NGliese/creditcard_cv_showoff/main/Components/lcd_display/include/lcd_data.hpp

#ifndef main_Components_lcd_display_include_lcd_data_hpp
#define main_Components_lcd_display_include_lcd_data_hpp

#include <stdint.h>


uint8_t HelloWorld[512] = {
0xFF, 0xFF, 0xFF, 0xFF, 0xFF, 0xFF, 0xFF, 0xFF, 0xFF, 0xFF, 0xFF, 0xFF, 0xFF, 0xFF, 0xFF, 0xFF,
0xFF, 0xFF, 0xFF, 0xFF, 0xFF, 0xFF, 0xFF, 0xFF, 0xFF, 0xFF, 0xFF, 0xFF, 0xFF, 0xFF, 0xFF, 0xFF,
0xFF, 0xFF, 0xFF, 0xFF, 0xFF, 0xFF, 0xFF, 0xFF, 0xFF, 0xFF, 0xFF, 0xFF, 0xFF, 0xFF, 0xFF, 0xFF,
0xFF, 0xFF, 0xFF, 0xFF, 0xFF, 0xFF, 0xFF, 0xFF, 0xFF, 0xFF, 0xFF, 0xFF, 0xFF, 0xFF, 0xFF, 0xFF,
0xFF, 0xFF, 0xFF, 0xFF, 0xFF, 0xFF, 0xFF, 0xFF, 0xFF, 0xFF, 0xFF, 0xFF, 0xFF, 0xFF, 0xFF, 0xFF,
0xFF, 0xFF, 0xFF, 0xFF, 0xFF, 0xFF, 0xFF, 0xFF, 0xFF, 0xFF, 0xFF, 0xFF, 0xFF, 0xFF, 0xFF, 0xFF,
0xFF, 0xFF, 0xFF, 0xFF, 0xFF, 0xFF, 0xFF, 0xFF, 0xFF, 0xFF, 0xFF, 0xFF, 0xFF, 0xFF, 0xFF, 0xFF,
0xFF, 0xFF, 0xFF, 0xFF, 0xFF, 0xFF, 0xFF, 0xFF, 0xFF, 0xFF, 0xFF, 0xFF, 0xFF, 0xFF, 0xFF, 0xFF,
0xFF, 0xFF, 0xFF, 0xFF, 0xFF, 0xFF, 0xFF, 0xFF, 0x07, 0x07, 0x07, 0x07, 0xC7, 0xC7, 0x07, 0x07,
0x07, 0x07, 0xC7, 0xC7, 0x07, 0x07, 0xC7, 0xC7, 0x47, 0x47, 0x4F, 0x4F, 0x0F, 0x0F, 0xCF, 0xCF,
0x0F, 0x0F, 0x0F, 0x0F, 0x0F, 0x0F, 0xCF, 0xCF, 0x0F, 0x0F, 0x0F, 0x0F, 0x0F, 0x0F, 0x8F, 0x8F,
0x4F, 0x4F, 0x4F, 0x8F, 0x0F, 0x0F, 0x0F, 0x0F, 0x0F, 0x0F, 0x0F, 0xCF, 0x8F, 0x0F, 0x0F, 0x8F,
0xCF, 0xCF, 0x0F, 0x0F, 0x0F, 0xCF, 0x0F, 0x0F, 0x0F, 0x87, 0x87, 0x47, 0x47, 0x47, 0x87, 0x07,
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
    {
        return pdata[icon%NUMBER_OF_ICONS];
    }
    private:
    uint8_t  *pdata[512] = {
        HelloWorld, stripes,star,name
    };
    const uint8_t NUMBER_OF_ICONS = 4; // number of icons in the array
};




#endif /*main_Components_lcd_display_include_lcd_data_hpp*/
